mlaiacker/soldering-station/doc/images/20151206_163124.jpg

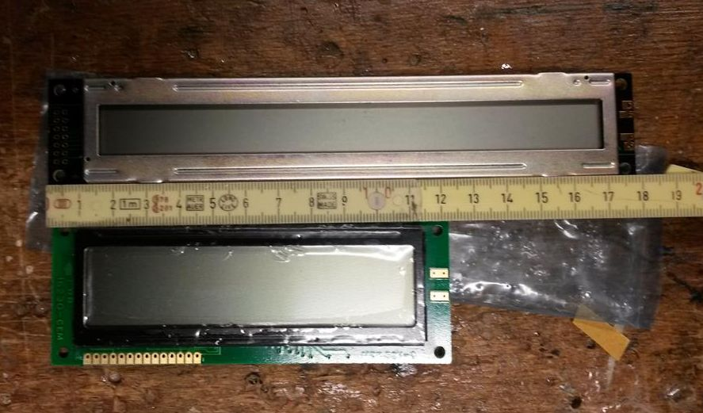
doc/images/20151206_163124.jpg
