mlaiacker/soldering-station/doc/images/IMG_4281.JPG

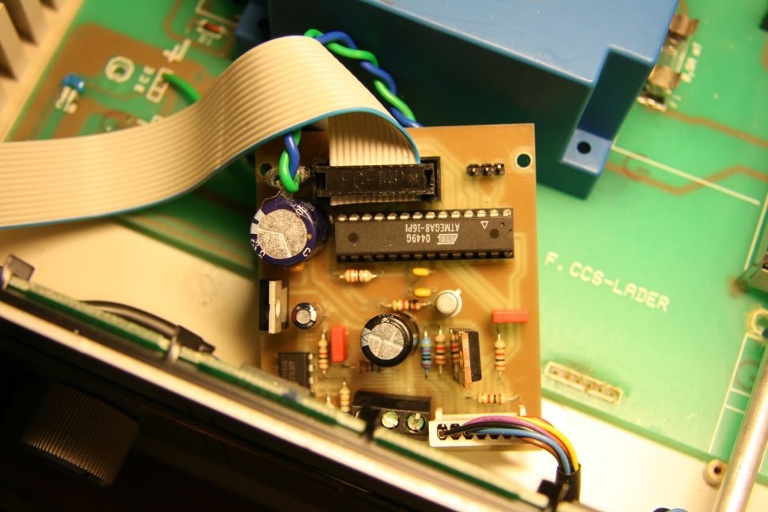
doc/images/IMG_4281.JPG
