mlaiacker/soldering-station/doc/images/IMG_4284.JPG

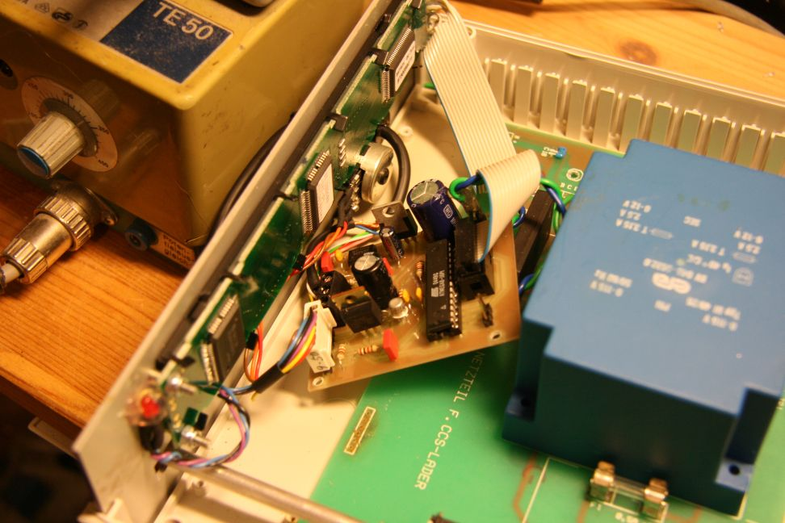
doc/images/IMG_4284.JPG
