mlaiacker/soldering-station/doc/images/img_20140726_142730.jpg

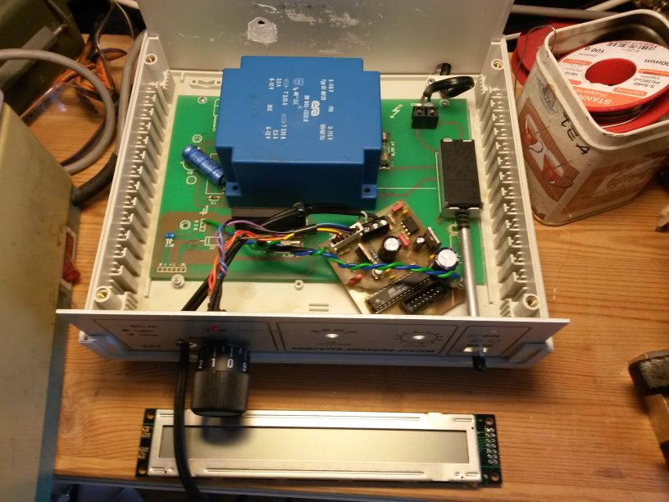
doc/images/img_20140726_142730.jpg
