mlaiacker/soldering-station/doc/images/img_20140730_225143.jpg

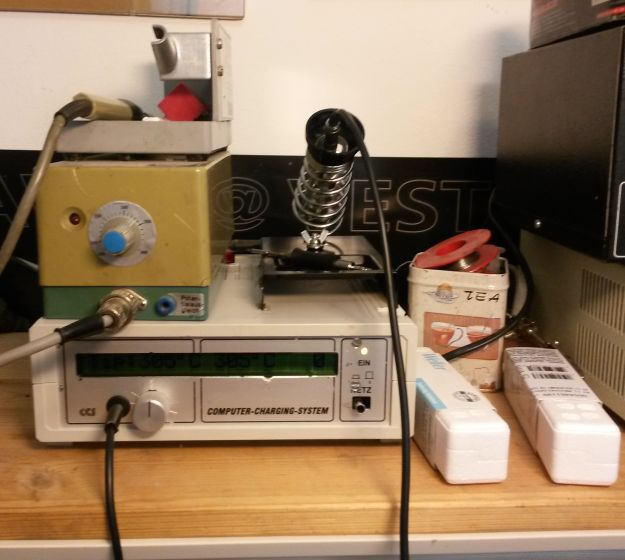
doc/images/img_20140730_225143.jpg
